VibrasticLab/pikoakustik/document/flyer_v1/alur_data.png

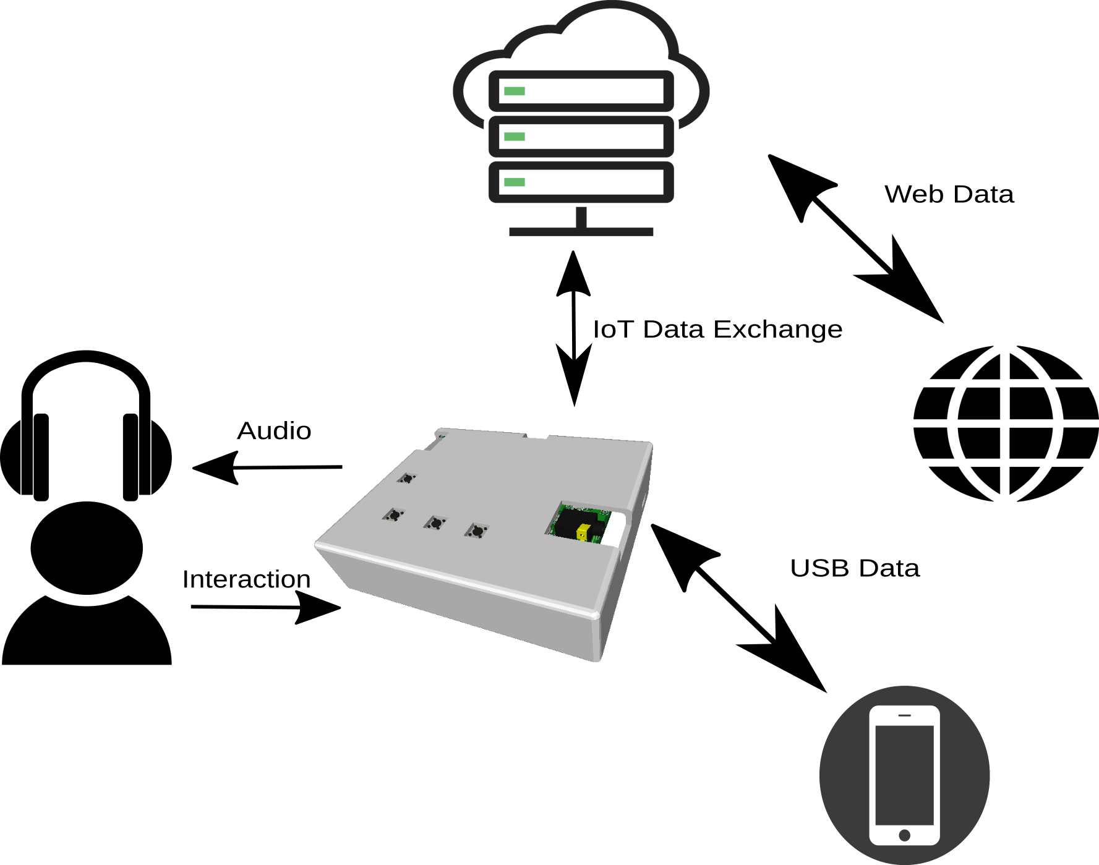
document/flyer_v1/alur_data.png
