VibrasticLab/pikoakustik/document/flyer_v1/images/headphone.png

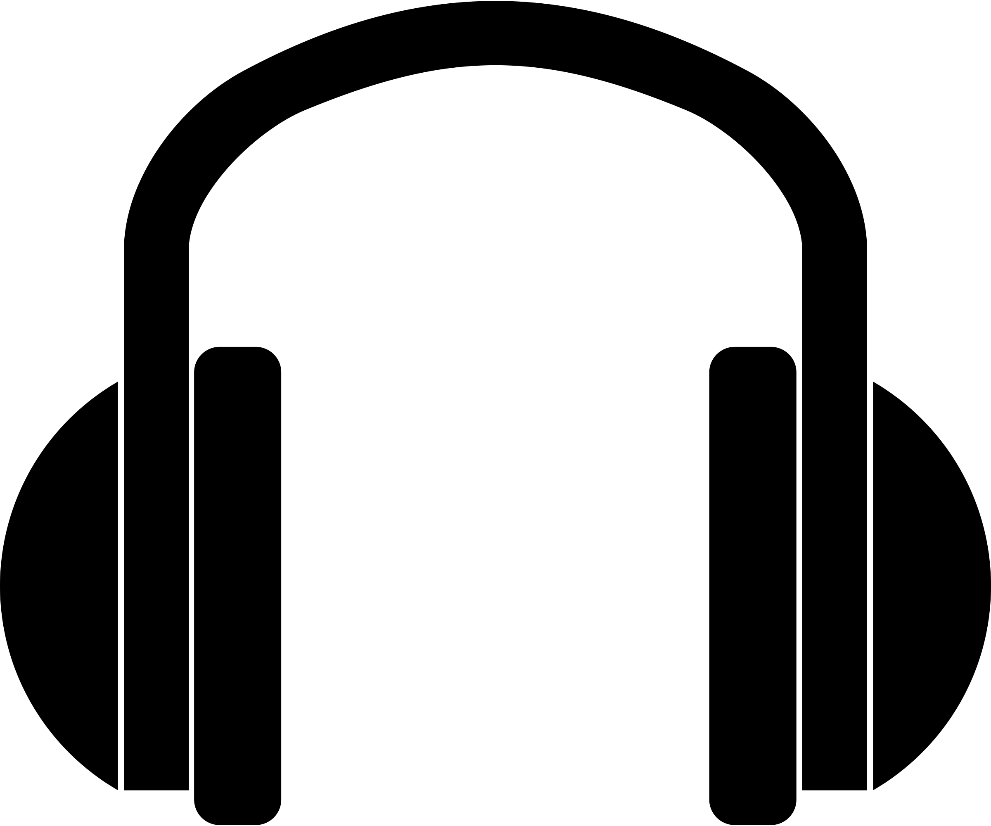
document/flyer_v1/images/headphone.png
