VibrasticLab/pikoakustik/document/flyer_v1/images/web.png

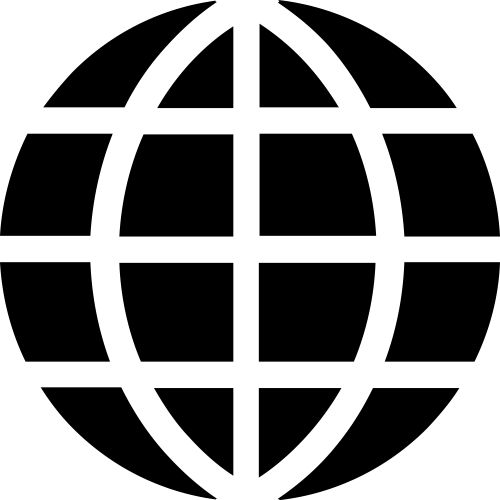
document/flyer_v1/images/web.png
