VibrasticLab/pikoakustik/document/flyer_v1/mockup.png

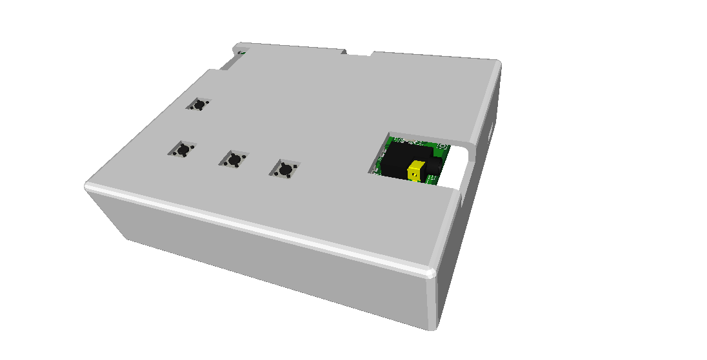
document/flyer_v1/mockup.png
