VibrasticLab/pikoakustik/document/license_patent2/images/model.png

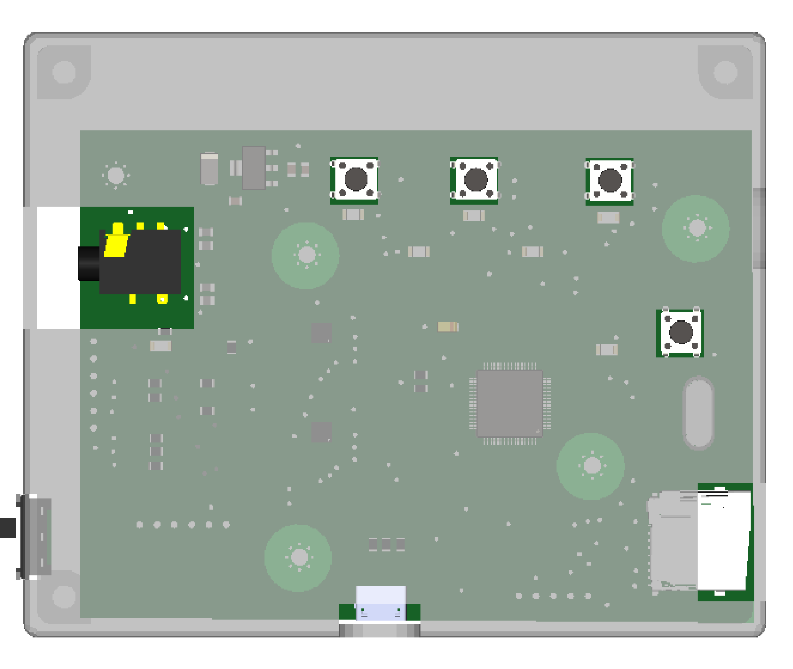
document/license_patent2/images/model.png
