VibrasticLab/pikoakustik/document/license_patent/images/chip.png

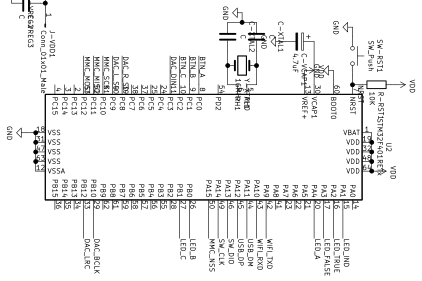
document/license_patent/images/chip.png
