VibrasticLab/pikoakustik/document/license_patent/images/dac.png

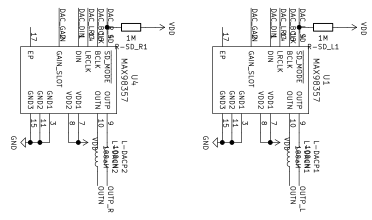
document/license_patent/images/dac.png
