VibrasticLab/pikoakustik/document/license_patent/images/layout.png

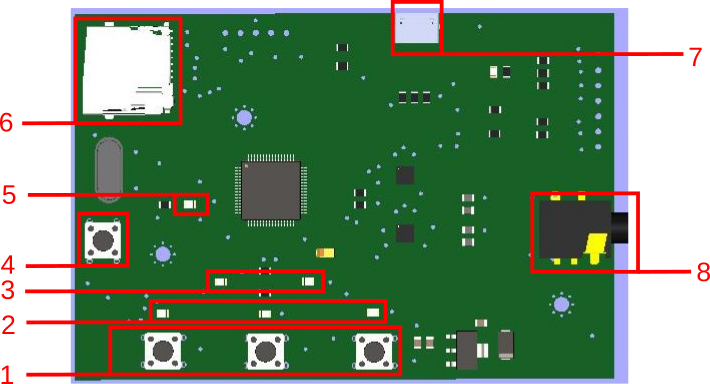
document/license_patent/images/layout.png
