VibrasticLab/pikoakustik/document/license_patent/images/ledbutton.jpg

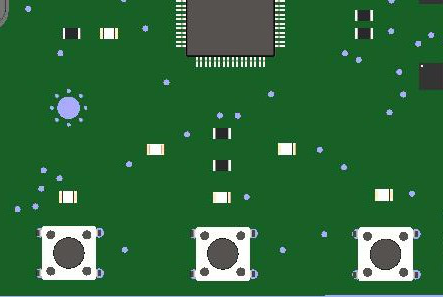
document/license_patent/images/ledbutton.jpg
