VibrasticLab/pikoakustik/document/license_patent/images/size.jpg

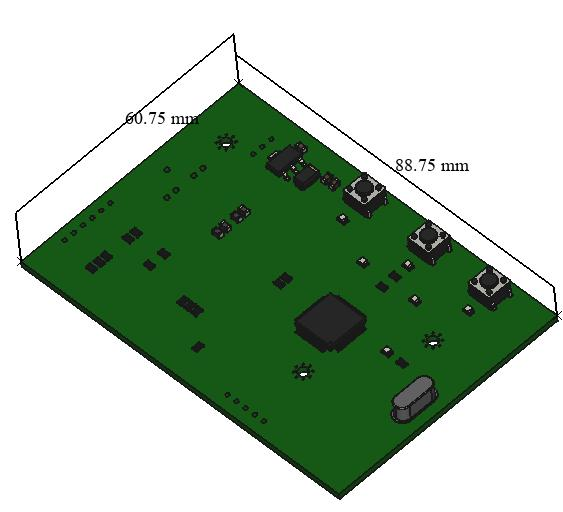
document/license_patent/images/size.jpg
