VibrasticLab/pikoakustik/document/symbol_sticker/mmc.png

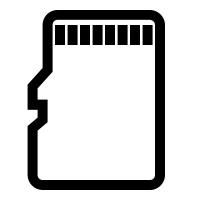
document/symbol_sticker/mmc.png
