VibrasticLab/pikoakustik/document/short_test/hasil_rpi/bose/1000/40.csv

FFT | Power Spectrum
Frequency[Hz] | Level-L[dB] | Level-R[dB]
11.719 | -3.8244 | -62.239
23.438 | 16.672 | -52.478
35.156 | 16.185 | -42.015
46.875 | 16.537 | -27.652
58.594 | 17.798 | -25.889
70.313 | 18.301 | -32.607
82.031 | 21.805 | -27.635
93.75 | 24.95 | -24.691
105.47 | 22.422 | -22.148
117.19 | 18.131 | -18.318
128.91 | 18.297 | -17.751
140.63 | 19.807 | -15.175
152.34 | 17.116 | -11.664
164.06 | 16.882 | -15.597
175.78 | 16.262 | -16.284
187.5 | 17.599 | -15.668
199.22 | 18.747 | -14.264
210.94 | 16.658 | -13.614
222.66 | 17.376 | -16.326
234.38 | 17.973 | -15.604
246.09 | 17.708 | -11.52
257.81 | 18.516 | -12.673
269.53 | 18.195 | -15.524
281.25 | 16.608 | -13.911
292.97 | 13.87 | -13.938
304.69 | 12.866 | -15.882
316.41 | 13.926 | -15.804
328.13 | 14.37 | -14.009
339.84 | 16.732 | -15.54
351.56 | 16.554 | -14.941
363.28 | 16.338 | -14.861
375 | 15.547 | -11.888
386.72 | 17.224 | -11.661
398.44 | 17.985 | -13.41
410.16 | 16.788 | -11.915
421.88 | 15.309 | -11.049
433.59 | 18.648 | -13.438
445.31 | 16.431 | -9.9764
457.03 | 19.721 | -10.166
468.75 | 21.083 | -10.96
480.47 | 16.578 | -11.097
492.19 | 17.093 | -13.849
503.91 | 14.163 | -9.6343
515.63 | 19.071 | -10.96
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
