VibrasticLab/pikoakustik/document/short_test/hasil_rpi/bose/1000/50.csv

FFT | Power Spectrum
Frequency[Hz] | Level-L[dB] | Level-R[dB]
11.719 | -4.4039 | -63.936
23.438 | 15.638 | -53.212
35.156 | 13.898 | -40.577
46.875 | 16.044 | -27.863
58.594 | 18.016 | -26.407
70.313 | 16.747 | -32.131
82.031 | 19.284 | -31.974
93.75 | 23.752 | -26.659
105.47 | 21.167 | -25.501
117.19 | 15.905 | -23.54
128.91 | 17.261 | -19.855
140.63 | 21.914 | -15.315
152.34 | 21.589 | -12.123
164.06 | 15.871 | -15.108
175.78 | 14.854 | -17.023
187.5 | 18.127 | -17.531
199.22 | 21.167 | -15.502
210.94 | 20.189 | -13.842
222.66 | 18.539 | -14.238
234.38 | 20.165 | -14.04
246.09 | 18.345 | -11.072
257.81 | 11.911 | -12.885
269.53 | 13.793 | -15.903
281.25 | 18.139 | -16.049
292.97 | 21.259 | -17.711
304.69 | 19.581 | -14.713
316.41 | 16.862 | -13.85
328.13 | 16.427 | -14.706
339.84 | 15.704 | -14.836
351.56 | 15.306 | -13.394
363.28 | 15.368 | -15.594
375 | 16.296 | -14.738
386.72 | 18.175 | -13.225
398.44 | 19.704 | -12.897
410.16 | 18.39 | -13.617
421.88 | 18.321 | -13.766
433.59 | 14.231 | -12.865
445.31 | 14.02 | -10.114
457.03 | 16.535 | -10.305
468.75 | 19.549 | -13.156
480.47 | 17.951 | -14.774
492.19 | 18.877 | -13.918
503.91 | 19.165 | -12.503
515.63 | 17.029 | -11.309
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
