VibrasticLab/pikoakustik/document/short_test/hasil_rpi/bose/1000/70.csv

FFT | Power Spectrum
Frequency[Hz] | Level-L[dB] | Level-R[dB]
11.719 | -4.9768 | -63.028
23.438 | 15.175 | -52.633
35.156 | 15.015 | -38.829
46.875 | 19.285 | -27.02
58.594 | 18.129 | -25.602
70.313 | 17.485 | -29.763
82.031 | 17.81 | -30.782
93.75 | 22.786 | -25.491
105.47 | 21.885 | -21.267
117.19 | 15.436 | -21.595
128.91 | 19.635 | -21.619
140.63 | 21.862 | -18.226
152.34 | 17.441 | -16.305
164.06 | 19.094 | -12.131
175.78 | 19.904 | -15.225
187.5 | 20.541 | -17.223
199.22 | 20.363 | -17.509
210.94 | 15.393 | -17.231
222.66 | 14.812 | -16.12
234.38 | 15.888 | -19.489
246.09 | 15.39 | -13.564
257.81 | 16.326 | -14.387
269.53 | 17.59 | -16.511
281.25 | 17.319 | -16.601
292.97 | 19.11 | -13.775
304.69 | 18.06 | -13.013
316.41 | 14.342 | -16.548
328.13 | 15.068 | -18.506
339.84 | 16.195 | -15.006
351.56 | 15.5 | -14.073
363.28 | 17.017 | -14.606
375 | 18.754 | -15.098
386.72 | 18.972 | -14.446
398.44 | 19.682 | -14.104
410.16 | 19.484 | -13.018
421.88 | 18.269 | -11.873
433.59 | 15.628 | -12.148
445.31 | 15.57 | -9.5718
457.03 | 17.963 | -10.675
468.75 | 16.432 | -12.656
480.47 | 16.613 | -9.1735
492.19 | 18.856 | -8.9784
503.91 | 18.708 | -11.142
515.63 | 19.956 | -8.2609
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
