VibrasticLab/pikoakustik/document/short_test/hasil_rpi/bose/1000/80.csv

FFT | Power Spectrum
Frequency[Hz] | Level-L[dB] | Level-R[dB]
11.719 | -5.6224 | -62.786
23.438 | 14.5 | -51.896
35.156 | 13.899 | -41.849
46.875 | 17.215 | -28.177
58.594 | 19.189 | -26.354
70.313 | 20.415 | -29.721
82.031 | 16.297 | -27.646
93.75 | 18.378 | -24.625
105.47 | 17.661 | -23.151
117.19 | 16.696 | -21.473
128.91 | 21.051 | -19.607
140.63 | 21.301 | -19.18
152.34 | 16.594 | -15.323
164.06 | 14.135 | -16.236
175.78 | 17.161 | -15.737
187.5 | 21.251 | -15.826
199.22 | 21.956 | -17.581
210.94 | 20.44 | -16.443
222.66 | 17.868 | -16.2
234.38 | 19.439 | -15.283
246.09 | 17.065 | -12.973
257.81 | 19.218 | -14.816
269.53 | 18.441 | -16.379
281.25 | 15.405 | -15.884
292.97 | 17.931 | -14.66
304.69 | 18.287 | -16.56
316.41 | 16.802 | -17.022
328.13 | 15.556 | -15.069
339.84 | 17.219 | -14.845
351.56 | 16.666 | -12.392
363.28 | 9.1076 | -13.113
375 | 17.133 | -9.9365
386.72 | 19.768 | -10.647
398.44 | 21.131 | -14.141
410.16 | 17.35 | -12.505
421.88 | 15.879 | -10.775
433.59 | 17.435 | -11.831
445.31 | 17.251 | -10.837
457.03 | 16.826 | -14.937
468.75 | 18.111 | -13.468
480.47 | 18.032 | -8.5509
492.19 | 14.531 | -9.4544
503.91 | 16.603 | -9.8459
515.63 | 19.669 | -11.129
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
