VibrasticLab/pikoakustik/document/test_kalibrasi/images/trs.png

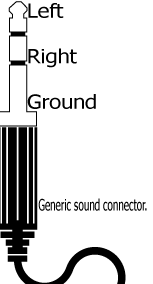
document/test_kalibrasi/images/trs.png
