VibrasticLab/pikoakustik/document/test_kalibrasi/images/hp_lrc/lrc.sch

## KiCad design document/test_kalibrasi/images/hp_lrc/lrc.sch (2020-08-01)

Schematic: lrc.sch

Parts:
L-LEFT1, L-LEFT2: L
L-RIGHT1, L-RIGHT2: L
LS-LEFT1: Speaker
LS-RIGHT1: Speaker
U1, U2: MAX98357
