VibrasticLab/pikoakustik/firmware/ht_comm.c

/*
    Embedded Audiometri - Copyright (C) 2020 Achmadi

    github.com/mekatronik-achmadi/ or mekatronik-achmadi@gmail.com

    Licensed under the Apache License, Version 2.0 (the "License");
    you may not use this file except in compliance with the License.
    You may obtain a copy of the License at

        http://www.apache.org/licenses/LICENSE-2.0

    Unless required by applicable law or agreed to in writing, software
    distributed under the License is distributed on an "AS IS" BASIS,
    WITHOUT WARRANTIES OR CONDITIONS OF ANY KIND, either express or implied.
    See the License for the specific language governing permissions and
    limitations under the License.
*/

/**
 * @file    ht_comm.c
 * @brief   Shell Commands code.
 *
 * @addtogroup Console
 * @{
 */

#include <stdio.h>
#include <stdlib.h>
#include <string.h>

#include "ch.h"
#include "hal.h"
#include "chprintf.h"

#include "user_conf.h"
#include "ht_console.h"
#include "ht_audio.h"
#include "ht_metri.h"
#include "ht_mmc.h"
#include "ht_led.h"

/* USB-CDC pointer object */
extern SerialUSBDriver SDU1;
extern const USBConfig usbcfg;
extern const SerialUSBConfig serusbcfg;

/* File related */
extern uint8_t lastnum;

/* Mode related */
extern uint8_t mode_status;
extern uint8_t channel_stt;
extern uint8_t mode_led;

/*******************************************
 * Serial Command Callback
 *******************************************/
/**
 * @brief Test command callback
 * @details Enumerated and not called directly by any normal thread
 */
static void cmd_coba(BaseSequentialStream *chp, int argc, char *argv[]){
    (void)argc;
    (void)argv;

    if (argc > 0) {
      chprintf(chp, "Usage: coba\r\n");
      return;
    }
    chprintf(chp,"Serial Console at %d & buffer size %d bit\r\n",SERIAL_DEFAULT_BITRATE,SERIAL_BUFFERS_SIZE);
}


/**
 * @brief Test command callback
 * @details Enumerated and not called directly by any normal thread
 */
static void cmd_test(BaseSequentialStream *chp, int argc, char *argv[]) {
    uint8_t lrc;

    chprintf(chp,"Playing Audio Test\r\n");

    if(argc==0){
#if USER_AUDIO
    chprintf(chp,"Test on both Channel\r\n");
    ht_audio_TestBoth();
#else
    chprintf(chp,"Audio features disabled\r\n");
#endif
    }
    else if(argc == 1){
#if USER_AUDIO
        lrc = atoi(argv[0]);
        ht_audio_Tone(1.25,1);

        if(lrc==OUT_LEFT){
            ht_audio_LeftCh();
            chprintf(chp,"Test on Left Channel\r\n");
            ht_audio_Play(TEST_DURATION);
            chThdSleepMilliseconds(200);
            ht_audio_Play(TEST_DURATION);
        }
        else if(lrc==OUT_RIGHT){
            ht_audio_RightCh();
            chprintf(chp,"Test on Right Channel\r\n");
            ht_audio_Play(TEST_DURATION);
            chThdSleepMilliseconds(200);
            ht_audio_Play(TEST_DURATION);
        }
        else{
            chprintf(chp,"Channel option incorrect \r\n");
        }
        ht_audio_DisableCh();
#else
        chprintf(chp,"Audio features disabled\r\n");
#endif
    }
    else{
        chprintf(chp,"usage: test [0|1] \r\n");
        chprintf(chp,"0 -> Left Channel \r\n");
        chprintf(chp,"1 -> Righ Channel \r\n");
        return;
    }
}

/*******************************************/

/**
 * @brief Audio Zero command callback
 * @details Enumerated and not called directly by any normal thread
 */
static void cmd_zero(BaseSequentialStream *chp, int argc, char *argv[]) {
    if(argc != 1){chprintf(chp,"usage: zero <0/1>\r\n");return;}

    uint8_t lrc = atoi(argv[0]);
    switch(lrc){
        case OUT_LEFT:
            ht_audio_LeftCh();
            chprintf(chp,"Left Channel on\r\n");
            break;

        case OUT_RIGHT:
            ht_audio_RightCh();
            chprintf(chp,"Right Channel on\r\n");
            break;
    }

    chprintf(chp,"Test Audio: Sine Zero\r\n");
    ht_audio_Tone(1.25,0);
    ht_audio_Play(TEST_DURATION);
    ht_audio_DisableCh();
    chprintf(chp,"Finished\r\n");
}

/**
 * @brief Audio Maximum command callback
 * @details Enumerated and not called directly by any normal thread
 */
static void cmd_max(BaseSequentialStream *chp, int argc, char *argv[]) {
    if(argc != 1){chprintf(chp,"usage: max <0/1>\r\n");return;}

    uint8_t lrc = atoi(argv[0]);
    switch(lrc){
        case OUT_LEFT:
            ht_audio_LeftCh();
            chprintf(chp,"Left Channel on\r\n");
            break;

        case OUT_RIGHT:
            ht_audio_RightCh();
            chprintf(chp,"Right Channel on\r\n");
            break;
    }

    chprintf(chp,"Test Audio: Sine Maximum\r\n");
    ht_audio_Tone(1.25,1);
    ht_audio_Play(TEST_DURATION);
    ht_audio_DisableCh();
    chprintf(chp,"Finished\r\n");
}

/**
 * @brief Audio Minimum command callback
 * @details Enumerated and not called directly by any normal thread
 */
static void cmd_min(BaseSequentialStream *chp, int argc, char *argv[]) {
    if(argc != 1){chprintf(chp,"usage: min <0/1>\r\n");return;}

    uint8_t lrc = atoi(argv[0]);
    switch(lrc){
        case OUT_LEFT:
            ht_audio_LeftCh();
            chprintf(chp,"Left Channel on\r\n");
            break;

        case OUT_RIGHT:
            ht_audio_RightCh();
            chprintf(chp,"Right Channel on\r\n");
            break;
    }

    chprintf(chp,"Test Audio: Sine Minimum\r\n");
    ht_audio_Tone(1.25,SMALLEST_DB);
    ht_audio_Play(TEST_DURATION);
    ht_audio_DisableCh();
    chprintf(chp,"Finished\r\n");
}

/**
 * @brief Audio Play at a frequency and amplitude at left/right channel
 * @details Enumerated and not called directly by any normal thread
 */
static void cmd_tone(BaseSequentialStream *chp, int argc, char *argv[]) {
    double vampl;
    double vfreq;
    uint8_t lrc = 0;
    uint16_t sing_durr = 500;

    if(argc==2){
        lrc = 0;
        vfreq = atof(argv[0]);
        vampl = atof(argv[1]);
    }
    else if(argc==3){
        lrc = atoi(argv[0]);
        vfreq = atof(argv[1]);
        vampl = atof(argv[2]);
    }
    else{
        chprintf(chp,"usage: tone <0/1> <freq> <ampl>\r\n");
        return;
    }

    switch(lrc){
        case OUT_LEFT:
            ht_audio_LeftCh();
            chprintf(chp,"Left Channel on\r\n");
            break;

        case OUT_RIGHT:
            ht_audio_RightCh();
            chprintf(chp,"Right Channel on\r\n");
            break;
    }

    if(vampl<=SMALLEST_DB){
        chprintf(chp,"Warning: Amplitude bellow smallest set\r\n");
    }

    chprintf(chp,"Tone: Freq:%6.3f Ampl:%6.3f\r\n",vfreq,vampl);
    ht_audio_Tone(vfreq,vampl);
    ht_audio_Play(sing_durr);
    chprintf(chp,"Finished\r\n");
    ht_audio_DisableCh();
}

/**
 * @brief Audio Play at a frequency and amplitude at left/right channel
 * @details Same as cmd_tone except using some real value and scaling
 * @details Enumerated and not called directly by any normal thread
 */
static void cmd_toneout(BaseSequentialStream *chp, int argc, char *argv[]) {
    uint8_t in_ampl;
    uint16_t in_freq;

    //double vampl=1;
    double vfreq=1;

    uint8_t lrc = 0;
    uint16_t sing_durr = 1000;

    if(argc==2){
        lrc = 0;
        in_freq = atoi(argv[0]);
        in_ampl = atoi(argv[1]);
    }
    else if(argc==3){
        lrc = atoi(argv[0]);;
        in_freq = atoi(argv[1]);
        in_ampl = atoi(argv[2]);
    }
    else if(argc==4){
        lrc = atoi(argv[0]);
        in_freq = atoi(argv[1]);
        in_ampl = atoi(argv[2]);
        sing_durr = atoi(argv[3]);
    }
    else{
        chprintf(chp,"usage: tone <0/1> <freq> <ampl> <duration_ms>\r\n");
        return;
    }

    switch(lrc){
        case OUT_LEFT:
            ht_audio_LeftCh();
            chprintf(chp,"Left Channel on\r\n");
            break;

        case OUT_RIGHT:
            ht_audio_RightCh();
            chprintf(chp,"Right Channel on\r\n");
            break;
    }

#if USER_METRI_16KHZ
    if(in_freq>=250 && in_freq<=16000){
#else
    if(in_freq>=250 && in_freq<=8000){
#endif
        vfreq = (double) in_freq/400; // Known array length as default frequency
    }
    else{
#if USER_METRI_16KHZ
        chprintf(chp,"frequency only between 250 and 16000\r\n");
#else
        chprintf(chp,"frequency only between 250 and 8000\r\n");
#endif
        return;
    }

    if(!(in_ampl>0 && in_ampl<10)){
        chprintf(chp,"amplitudo scaling only between 1 and 9\r\n");
        return;
    }

#if USER_SER_SCALE
    ht_audio_ToneScale(vfreq, in_ampl);
    chprintf(chp,"Tone: Freq:%5i Ampl:%2i\r\n",in_freq,in_ampl);
#else
    switch(in_ampl){
        case 9: vampl=1;break;
        case 8: vampl=0.5;break;
        case 7: vampl=0.25;break;
        case 6: vampl=0.125;break;
        case 5: vampl=0.0625;break;
        case 4: vampl=0.0312;break;
        case 3: vampl=0.0156;break;
        case 2: vampl=0.0078;break;
        case 1: vampl=0.0039;break;
    }
    ht_audio_Tone(vfreq,vampl);
    chprintf(chp,"Tone: Freq:%6.3f Ampl:%6.3f\r\n",vfreq,vampl);
#endif

    ht_audio_Play(sing_durr);
    chprintf(chp,"Finished\r\n");
    ht_audio_DisableCh();
}

/**
 * @brief Audio Play at a frequency and down from highest to lowest amplitude
 * @details Enumerated and not called directly by any normal thread
 */
static void cmd_sing(BaseSequentialStream *chp, int argc, char *argv[]) {
    double vampl = 1;
    double vfreq = 1.25;
    uint8_t lrc = 0;
    uint16_t sing_durr = 500;

    if(argc == 0){
        lrc = 0;
        vfreq = 1.25;
    }
    else if(argc == 1){
        lrc = 0;
        vfreq = atof(argv[0]);
    }
    else if(argc == 2){
        lrc = atoi(argv[0]);
        vfreq = atof(argv[1]);
    }
    else{
        chprintf(chp,"usage: sing <0/1> <freq>\r\n");return;
    }

    switch(lrc){
        case OUT_LEFT:
            ht_audio_LeftCh();
            chprintf(chp,"Left Channel on\r\n");
            break;

        case OUT_RIGHT:
            ht_audio_RightCh();
            chprintf(chp,"Right Channel on\r\n");
            break;
    }

    while(1){
        chprintf(chp,"Sing: Freq:%6.3f Ampl:%6.3f\r\n",vfreq,vampl);
        ht_audio_Tone(vfreq,vampl);
        ht_audio_Play(sing_durr);
        chThdSleepMilliseconds(500);

        vampl = vampl/2;
        if(vampl<SMALLEST_DB){
            chprintf(chp,"Finished\r\n");
            break;
        }
    }
    ht_audio_DisableCh();
}

/**
 * @brief Speaker test using twice tone
 * @details Enumerated and not called directly by any normal thread
 */
static void cmd_sptest(BaseSequentialStream *chp, int argc, char *argv[]) {
    uint8_t lrc;

    if(argc != 1){chprintf(chp,"usage: sptest <0/1/2>\r\n");return;}

    lrc = atoi(argv[0]);

    switch(lrc){
        case 0: chprintf(chp,"Testing Left Channel\r\n"); ht_audio_TestLeft();break;
        case 1: chprintf(chp,"Testing Right Channel\r\n"); ht_audio_TestRight();break;
        case 2: chprintf(chp,"Testing Both Channel\r\n"); ht_audio_TestBoth();break;
    }
}

/*******************************************/

/**
 * @brief List available files on MMC and get saves last number
 * @details Enumerated and not called directly by any normal thread
 */
static void cmd_lsfile(BaseSequentialStream *chp, int argc, char *argv[]) {
    (void) argv;
    if(argc != 0){chprintf(chp,"usage: ls\r\n");return;}

    ht_mmc_lsFiles();
}

/**
 * @brief List available number files on MMC and get saves last number
 * @details Enumerated and not called directly by any normal thread
 */
static void cmd_lsnumfile(BaseSequentialStream *chp, int argc, char *argv[]) {
    (void) argv;
    if(argc != 0){chprintf(chp,"usage: ls\r\n");return;}

    ht_mmc_lsNumFiles();
}

/**
 * @brief CAT content file on given number suffix
 * @details Enumerated and not called directly by any normal thread
 */
static void cmd_catfile(BaseSequentialStream *chp, int argc, char *argv[]) {
    (void) argv;
    uint16_t fnum;

    if(argc==0 || argc>1){chprintf(chp,"usage: cat file_number\r\n");return;}
    fnum = atoi(argv[0]);
    ht_mmc_catFiles(fnum);
}

/**
 * @brief MMC Write Test command callback
 * @details Enumerated and not called directly by any normal thread
 */
static void cmd_mmcwrt(BaseSequentialStream *chp, int argc, char *argv[]) {
    (void) argv;
    if(argc != 0){chprintf(chp,"usage: mmcwr\r\n");return;}

    ht_mmc_Test();
    chprintf(chp,"MMC R/W Test Finished\r\n\r\n");
}

/**
 * @brief MMC CAT Test command callback
 * @details Enumerated and not called directly by any normal thread
 */
static void cmd_mmcat(BaseSequentialStream *chp, int argc, char *argv[]) {
    (void) argv;
    if(argc != 0){chprintf(chp,"usage: mmcat\r\n");return;}

    ht_mmc_catTest();
    chprintf(chp,"MMC R/W Content look Finished\r\n\r\n");
}

/**
 * @brief MMC Check Test command callback
 * @details Enumerated and not called directly by any normal thread
 */
static void cmd_mmchk(BaseSequentialStream *chp, int argc, char *argv[]) {
    (void) argv;
    if(argc != 0){chprintf(chp,"usage: mmchk\r\n");return;}

    ht_mmc_initCheck();
    chprintf(chp,"MMC Checking Finished\r\n\r\n");
}

/**
 * @brief MMC Files Clear command callback
 * @details Enumerated and not called directly by any normal thread
 */
static void cmd_mmclr(BaseSequentialStream *chp, int argc, char *argv[]) {
    (void) argv;
    if(argc != 0){chprintf(chp,"usage: mmchk\r\n");return;}

    chprintf(chp,"MMC files clearing\r\n\r\n");
    ht_mmc_delAllFiles();
}

/*******************************************/

/**
 * @brief Memory check function
 * @details Enumerated and not called directly by any normal thread
 */
static void cmd_chmem(BaseSequentialStream *chp, int argc, char *argv[]) {
  size_t n, size;

  (void)argv;
  if (argc > 0) {
    chprintf(chp, "Usage: mem\r\n");
    return;
  }
  n = chHeapStatus(NULL, &size);
  chprintf(chp, "core free memory : %u bytes\r\n", chCoreGetStatusX());
  chprintf(chp, "heap fragments   : %u\r\n", n);
  chprintf(chp, "heap free total  : %u bytes\r\n", size);
}

/**
 * @brief Thread check function
 * @details Enumerated and not called directly by any normal thread
 */
static void cmd_chthds(BaseSequentialStream *chp, int argc, char *argv[]) {
  static const char *states[] = {CH_STATE_NAMES};
  thread_t *tp;

  (void)argv;
  if (argc > 0) {
    chprintf(chp, "Usage: chthds\r\n");
    return;
  }
  chprintf(chp, "    addr    stack prio refs     state time\r\n");
  tp = chRegFirstThread();
  do {
    chprintf(chp, "%08lx %08lx %4lu %4lu %9s\r\n",
            (uint32_t)tp, (uint32_t)tp->p_ctx.r13,
            (uint32_t)tp->p_prio, (uint32_t)(tp->p_refs - 1),
            states[tp->p_state]);
    tp = chRegNextThread(tp);
  } while (tp != NULL);
}

/*******************************************/

/**
 * @brief Tester name check function
 * @details Enumerated and not called directly by any normal thread
 */
static void cmd_who(BaseSequentialStream *chp, int argc, char *argv[]) {

  (void)argv;
  if (argc > 0) {
    chprintf(chp, "Usage: who\r\n");
    return;
  }

  char tester[] = USER_TESTER;
  chprintf(chp, "tester name: \"%s\"\r\n",tester);
}

/**
 * @brief Run Virtual Test
 * @details Enumerated and not called directly by any normal thread
 */
static void cmd_virt(BaseSequentialStream *chp, int argc, char *argv[]) {
    (void)argv;
    if (argc > 0) {
      chprintf(chp, "Usage: virt\r\n");
      return;
    }

    chprintf(chp, "Run Virtual Test Start\r\n");
    chprintf(chp, "DONT PUSH ANY BUTTON\r\n");

    ht_mmcMetri_chkFile();
    ht_mmcMetri_jsonChStart(channel_stt);

    mode_led = LED_METRI;
    mode_status = STT_VIRT;
}

/*******************************************/

/**
 * @brief Shell command and it's callback enumeration
 * @details Extending from internal shell's callback
 */
static const ShellCommand commands[] = {
    {"coba",cmd_coba},
    {"test",cmd_test},
    {"virt",cmd_virt},
    {"who",cmd_who},
#if USER_AUDIO
    {"zero",cmd_zero},
    {"sing",cmd_sing},
    {"tone",cmd_tone},
    {"max",cmd_max},
    {"min",cmd_min},
    {"out",cmd_toneout},
    {"sptest",cmd_sptest},
#endif
#if USER_MMC
    {"ls",cmd_lsfile},
    {"lsnum",cmd_lsnumfile},
    {"cat",cmd_catfile},
    {"mmcwr",cmd_mmcwrt},
    {"mmcat",cmd_mmcat},
    {"mmchk",cmd_mmchk},
    {"mmclr",cmd_mmclr},
#endif
    {"chmem",cmd_chmem},
    {"chthds",cmd_chthds},
    {NULL, NULL}
};

/*******************************************
 * Serial Peripheral Setup
 *******************************************/

/**
 * @brief UART Shell Console pointer
 */
static thread_t *shelltp_uart = NULL;

/**
 * @brief USB Shell Console pointer
 */
static thread_t *shelltp_usb = NULL;

/**
 * @brief Shell Driver Config
 * @details Serial Interface using UART1 (SD1)
 */
static const ShellConfig shell_uart_cfg = {
  (BaseSequentialStream *)&SD1,
  commands
};

/**
 * @brief Shell Driver Config
 * @details Serial Interface using USB1 (SDU1)
 */
static const ShellConfig shell_usb_cfg = {
  (BaseSequentialStream *)&SDU1,
  commands
};

void ht_commUART_Init(void){
    palSetPadMode(GPIOA, 9,PAL_MODE_ALTERNATE(7) | PAL_STM32_OSPEED_HIGHEST); //TX
    palSetPadMode(GPIOA,10,PAL_MODE_ALTERNATE(7) | PAL_STM32_OSPEED_HIGHEST); //RX
    sdStart(&SD1,NULL);

    shellInit();
}

void ht_commUSB_Init(void){
    sduObjectInit(&SDU1);
    sduStart(&SDU1, &serusbcfg);

    usbDisconnectBus(serusbcfg.usbp);
    usbStop(serusbcfg.usbp);
    chThdSleepMilliseconds(500);
    usbStart(serusbcfg.usbp, &usbcfg);
    usbConnectBus(serusbcfg.usbp);

    shellInit();
}

void ht_commUART_shInit(void){
    if (!shelltp_uart) {
        shelltp_uart = shellCreate(&shell_uart_cfg, SHELL_WA_SIZE, NORMALPRIO);
    }
    else {
        if (chThdTerminatedX(shelltp_uart)) {
            chThdRelease(shelltp_uart);
            shelltp_uart = NULL;
        }
    }
}

void ht_commUSB_shInit(void){
    if (!shelltp_usb && (SDU1.config->usbp->state == USB_ACTIVE)) {
        shelltp_usb = shellCreate(&shell_usb_cfg, SHELL_WA_SIZE, NORMALPRIO);
    }
    else {
        if (chThdTerminatedX(shelltp_usb)) {
            chThdRelease(shelltp_usb);
            shelltp_usb = NULL;
        }
    }
}

void ht_comm_Msg(char *string){
    if(SDU1.config->usbp->state == USB_ACTIVE){
        chprintf((BaseSequentialStream *)&SDU1,string);
    }
}

void ht_comm_IoT(char *string){
    chprintf((BaseSequentialStream *)&SD1,string);
}

/** @} */
