VibrasticLab/pikoakustik/esp8266/esp_mqtt/user/mqtt_client.c

#include "ets_sys.h"
#include "osapi.h"
#include "mqtt.h"
#include "user_interface.h"
#include "mem.h"

extern os_timer_t blinky_timer;

MQTT_Client mqttClient;
os_timer_t mqttcon_timer;

/**
 * @brief MQTT connected led
 */
LOCAL uint8 led_mqtt_connect = 0;

LOCAL void mqttConnectedCb(uint32_t *args){
    MQTT_Client* client = (MQTT_Client*)args;
    os_printf("MQTT: Connected\r\n");

    os_timer_disarm(&mqttcon_timer);
    MQTT_Subscribe(client, "metri/audio", 0);

    os_timer_disarm(&blinky_timer);
    os_timer_arm(&blinky_timer, 50, 1);
}

LOCAL void mqttDisconnectedCb(uint32_t *args){
    MQTT_Client* client = (MQTT_Client*)args;
    os_printf("MQTT: Disconnected\r\n");

    os_timer_arm(&mqttcon_timer, 1000, 1);

    os_timer_disarm(&blinky_timer);
    os_timer_arm(&blinky_timer, 500, 1);
}

LOCAL void mqttPublishedCb(uint32_t *args){
    MQTT_Client* client = (MQTT_Client*)args;
    os_printf("MQTT: Published\r\n");
}

LOCAL void mqttDataCb(uint32_t *args, const char* topic, uint32_t topic_len, const char *data, uint32_t data_len){
    char *topicBuf = (char*)os_zalloc(topic_len+1),
            *dataBuf = (char*)os_zalloc(data_len+1);

    MQTT_Client* client = (MQTT_Client*)args;

    os_memcpy(topicBuf, topic, topic_len);
    topicBuf[topic_len] = 0;

    os_memcpy(dataBuf, data, data_len);
    dataBuf[data_len] = 0;

    os_printf("Receive topic: %s, data: %s \r\n", topicBuf, dataBuf);
    os_free(topicBuf);
    os_free(dataBuf);
}

/**
 * @brief MQTT Re-Init
 */
LOCAL void ICACHE_FLASH_ATTR mqttreinit_timer_handler(void *prv){
    os_printf("trying connecting broker\r\n");

    MQTT_InitConnection(&mqttClient, "192.168.43.1", 1883, 0);
    MQTT_InitClient(&mqttClient, "esp8266", NULL, NULL, 120, 0);

    MQTT_OnConnected(&mqttClient, mqttConnectedCb);
    MQTT_OnDisconnected(&mqttClient, mqttDisconnectedCb);
    MQTT_OnPublished(&mqttClient, mqttPublishedCb);
    MQTT_OnData(&mqttClient, mqttDataCb);
}

void mqttWifiConnectCb(uint8_t status){
    if(status == STATION_GOT_IP){
        MQTT_Connect(&mqttClient);
    }
    else {
        MQTT_Disconnect(&mqttClient);
    }
}

void mqttClientInit(void){
    os_timer_setfn(&mqttcon_timer, (os_timer_func_t *)mqttreinit_timer_handler, NULL);
    os_timer_arm(&mqttcon_timer, 1000, 1);
}
