VibrasticLab/pikoakustik/simulasi/fftgraph/simulasi.py

#!/usr/bin/env python
# -*- coding: utf-8 -*-
#
#  audiobar.py
#
#  Copyright 2021 achmaday <achmaday@archmate>
#
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
#

import sys
import numpy as np
import sounddevice as sd

from PyQt5.QtCore import QThread, pyqtSignal
from PyQt5.QtWidgets import QApplication, QDialog, QProgressBar, QPushButton

class Audio(QThread):

    dbSPL = pyqtSignal(int)
    vol_normL = 0
    vol_normR = 0
    gain = 100

    def print_level(self,indata, frames, time, status):
        self.vol_normL = int(np.linalg.norm(indata[:,0])*self.gain)
        self.vol_normR = int(np.linalg.norm(indata[:,1])*self.gain)
        vol_norm = int(np.linalg.norm(indata)*self.gain)
        self.dbSPL.emit(vol_norm)

    def run(self):
        with sd.InputStream(callback=self.print_level):
            print("input capture started")
            while True:
                pass
            print("input capture finished")

class Actions(QDialog):
    """docstring for Actions"""
    def __init__(self):
        super().__init__()
        self.initUI()

    def initUI(self):
        self.setWindowTitle('Audio Bar')
        self.vbarL = QProgressBar(self)
        self.vbarL.setGeometry(0,0,300,25)
        self.vbarL.setMaximum(100)

        self.vbarR = QProgressBar(self)
        self.vbarR.setGeometry(0,0,300,25)
        self.vbarR.setMaximum(100)
        self.vbarR.move(0, 30)

        self.show()

        sd.default.device = 2, None
        sd.default.channels = 2, None
        print(sd.query_devices())

        self.spl = Audio()
        self.spl.dbSPL.connect(self.onSPLchanged)
        self.spl.start()

    def onSPLchanged(self,value):
        spl_avg = value
        self.vbarL.setValue(self.spl.vol_normL)
        self.vbarR.setValue(self.spl.vol_normR)

if __name__ == '__main__':
    app = QApplication(sys.argv)
    wndw = Actions()
    sys.exit(app.exec_())
